gregdavill/GlassUnicorn/docs/images/IMG_0050.jpg

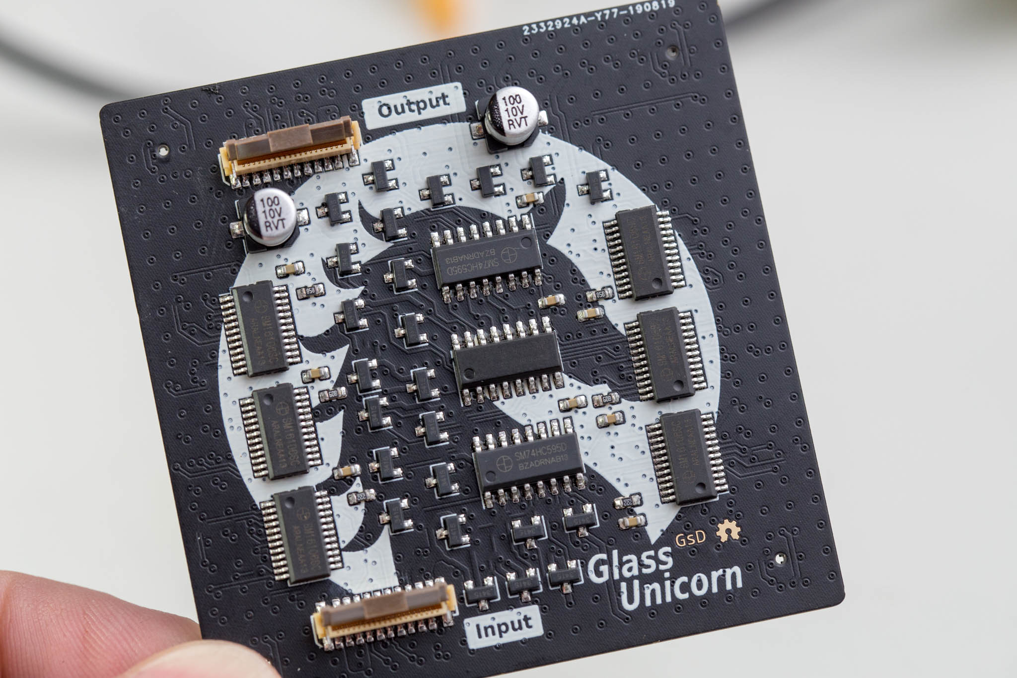
docs/images/IMG_0050.jpg
