gregdavill/GlassUnicorn/docs/images/IMG_0147.jpg

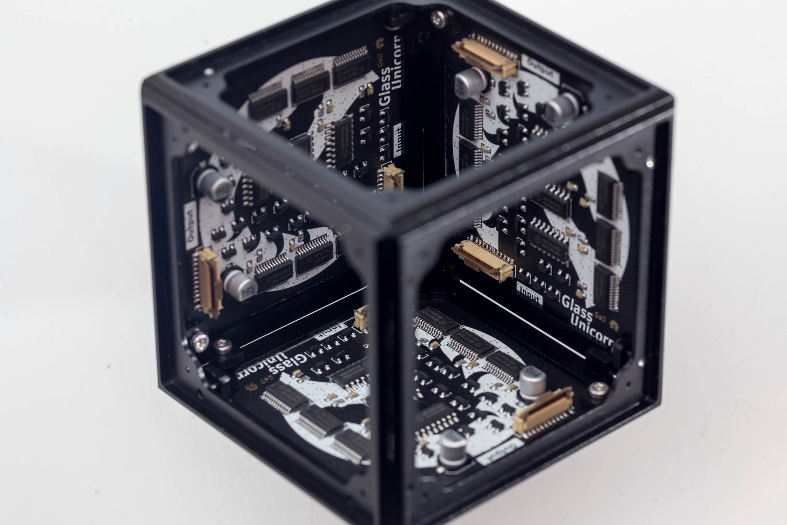
docs/images/IMG_0147.jpg
