gregdavill/GlassUnicorn/ref/artwork_32x32_1515.png

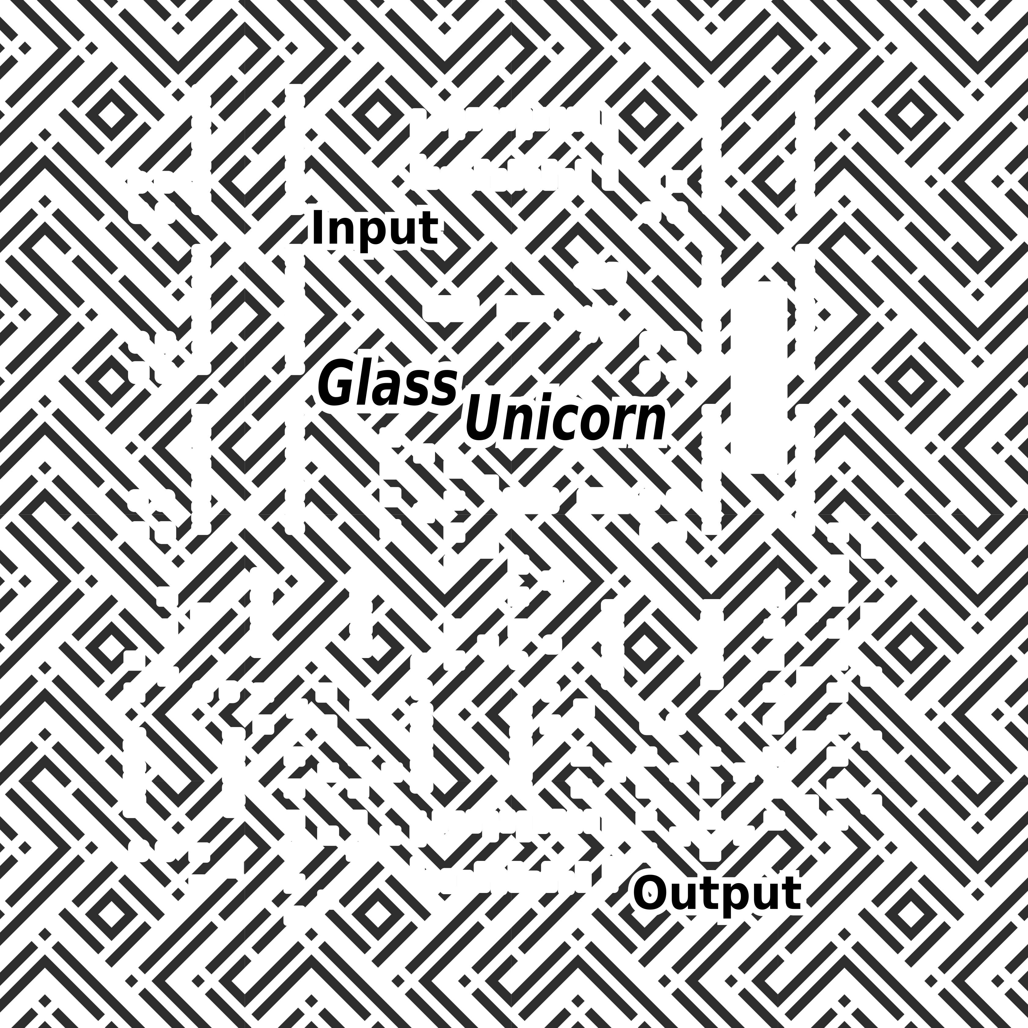
ref/artwork_32x32_1515.png
